tlchandler/PixelPlus/crates/pixelplus-daemon/testdata/reports/night-2026-12-01.html

Chandler <Lights> · nightly report

# Tuesday, Dec 1

⚠️ Mostly fine

2 shows, 2 songs, 3 requests, 2 problems.

2 Shows | 2 Songs | 3 Requests | 6h 00m Show time

## Problems

● | Garage reached 58 °C | ×1
● | <script>alert(1)</script> & more | ×1

## Shows

Show | Started | Minutes
Weeknights | 5:00 PM | 300
Late show | 11:30 PM | 60

## Most requested

All I Want | 2
Wizards in Winter | 1

## Controllers

Controller | Temp | Sync p95 | Offline
Main Controller | 40–44 °C | — | —
Garage | — | 1.1 ms | 4 min

## Lights

- Arch 2: suspect pixel 37
- Power limiter on Garage port 3: 15 s

## Housekeeping

- Disk: 71 % free
- Newest backup: 1 day old
- Visitors played 1 game (2 min)
- Triggers and sensors fired 1 time
- Updated 1.4.0 → 1.4.1
- PixelPlus restarted 2 times

Open the full report (http://pixelplus.local/reports?date=2026-12-01)

Sent by PixelPlus. Change or turn off in Settings → Nightly report.
