tlchandler/PixelPlus/boardtempinfo/diffrx/render_bottom.png

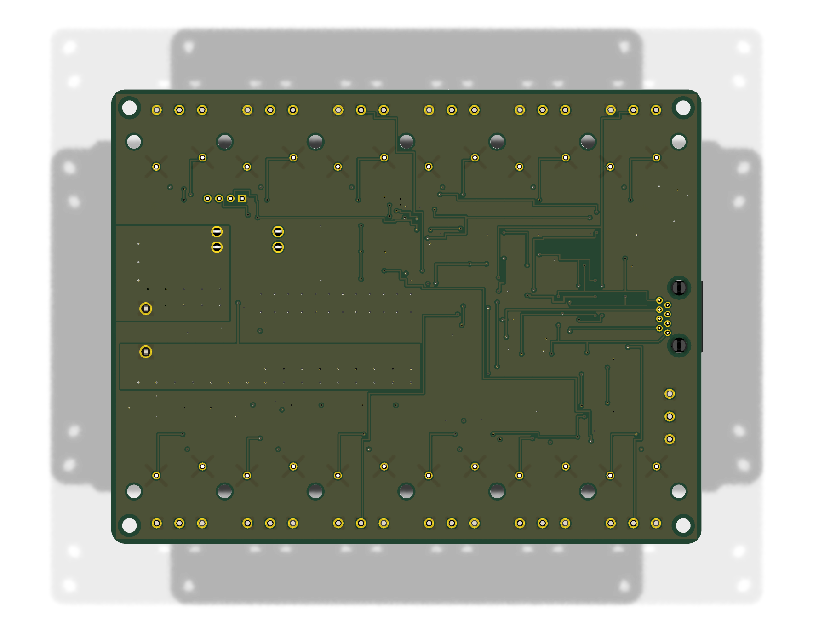
boardtempinfo/diffrx/render_bottom.png
