tlchandler/PixelPlus/boardtempinfo/difftx/render_bottom.png

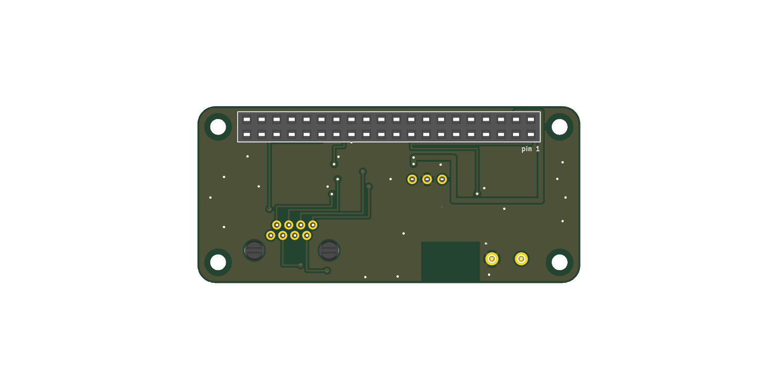
boardtempinfo/difftx/render_bottom.png
