tlchandler/PixelPlus/boardtempinfo/difftx/render_iso.png

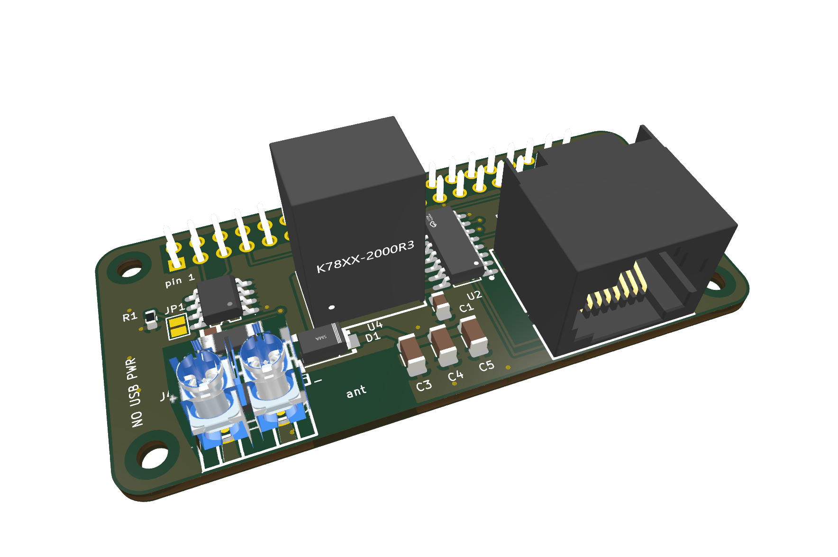
boardtempinfo/difftx/render_iso.png
