tlchandler/PixelPlus/boardtempinfo/difftxlarge/render_bottom.png

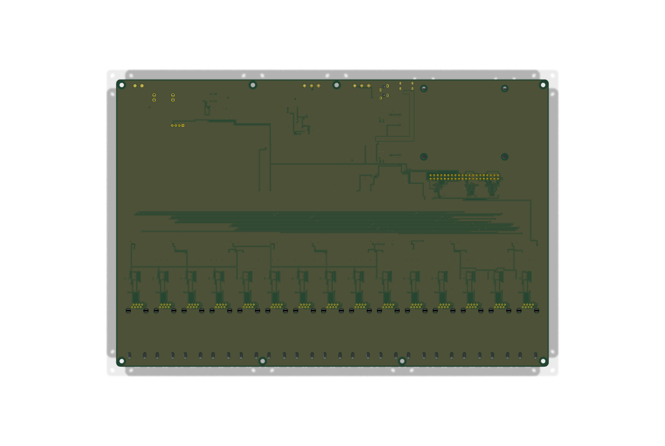
boardtempinfo/difftxlarge/render_bottom.png
