tlchandler/PixelPlus/boardtempinfo/difftxlarge/render_top.png

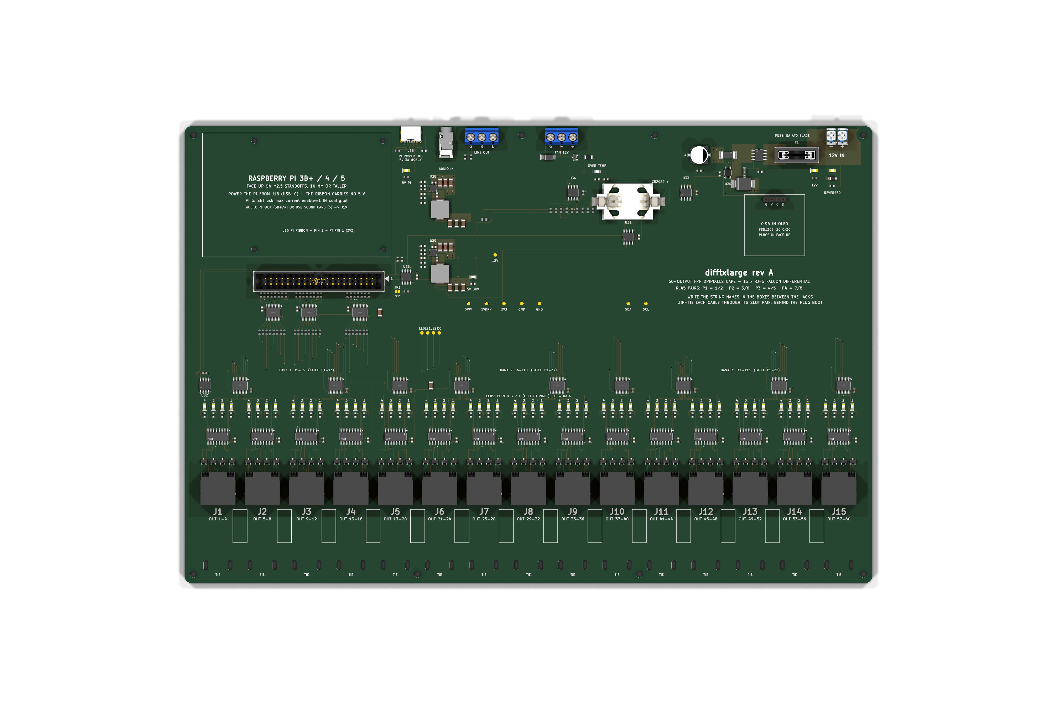
boardtempinfo/difftxlarge/render_top.png
